jblezoray/hpdl1414-watch/hpdl-1414/src/states/StateShowDate.h

#ifndef StateShowDate_h
#define StateShowDate_h

#include "state-manager/AbstractState.h"
#include "state-manager/Context.h"
#include "mixins/MixinTimeoutToScreenOff.h"
#include "mixins/MixinMoveToSetTemperature.h"
#include "mixins/MixinMoveToSetYear.h"

class StateShowDate : public MixinTimeoutToScreenOff,
                      public MixinMoveToSetTemperature,
                      public MixinMoveToSetYear {
  public:
    StateShowDate();
    void on_enter(Context * context);
    void in_loop(Context * context);
    void on_exit(Context * context);
};

#endif
